ernesto-g/mini_piano/Pictures/1.jpg

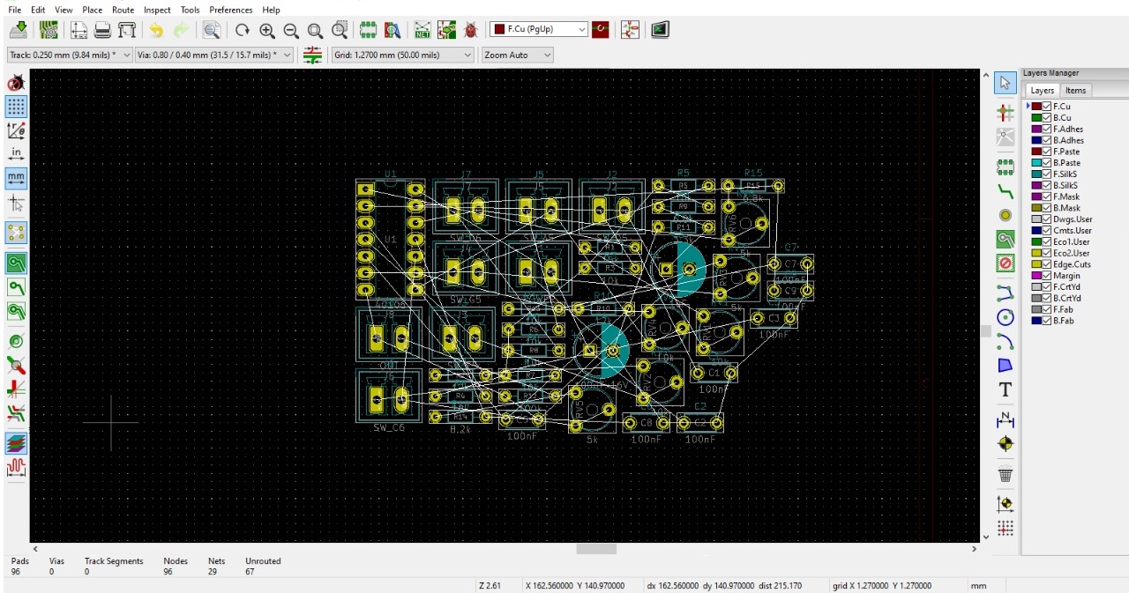
Pictures/1.jpg
