ernesto-g/mini_piano/Pictures/2.jpg

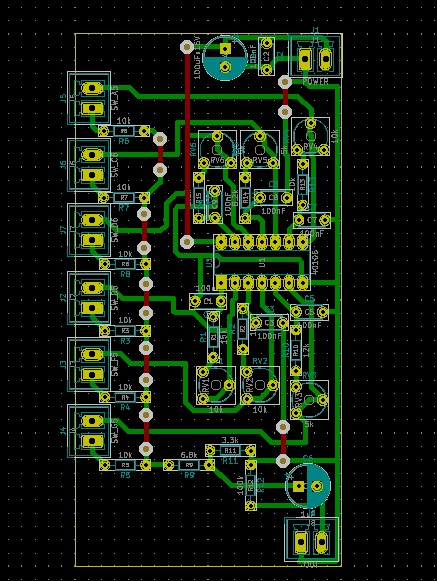
Pictures/2.jpg
