ernesto-g/mini_piano/Pictures/IMG_20210108_180527709.jpg

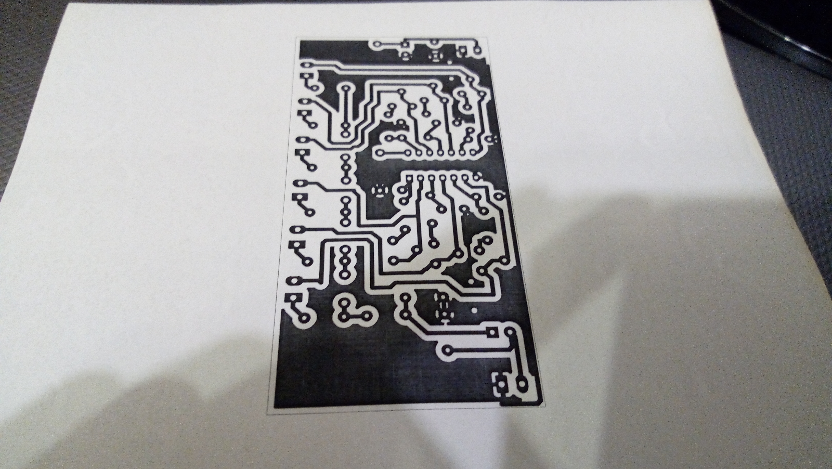
Pictures/IMG_20210108_180527709.jpg
