ernesto-g/mini_piano/Pictures/IMG_20210108_180604123.jpg

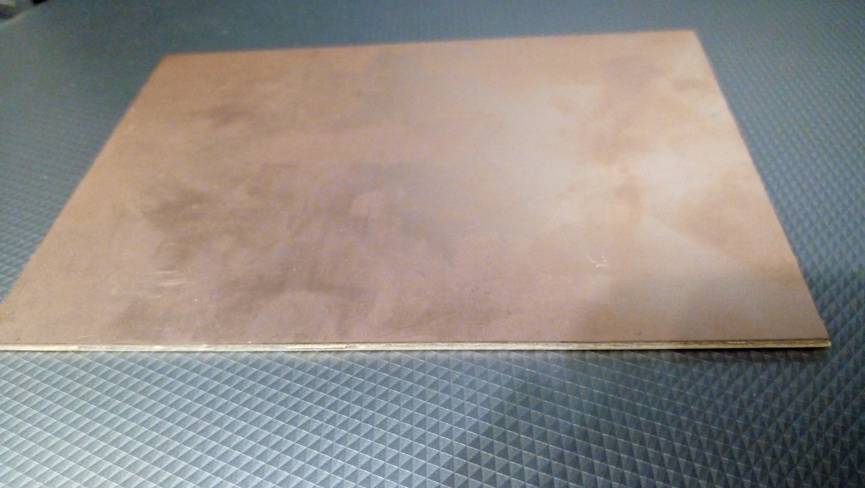
Pictures/IMG_20210108_180604123.jpg
