ernesto-g/mini_piano/Pictures/IMG_20210108_181249977.jpg

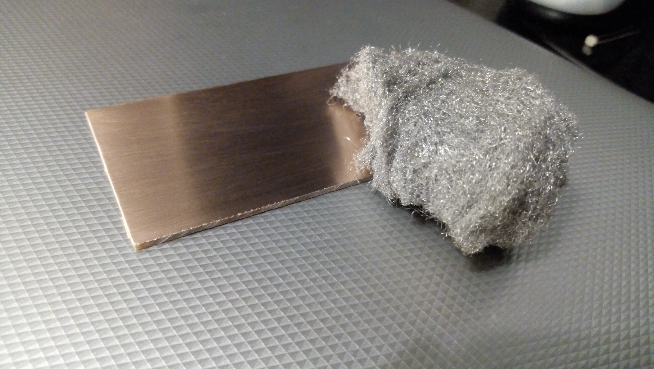
Pictures/IMG_20210108_181249977.jpg
