ernesto-g/mini_piano/Pictures/IMG_20210108_181337347.jpg

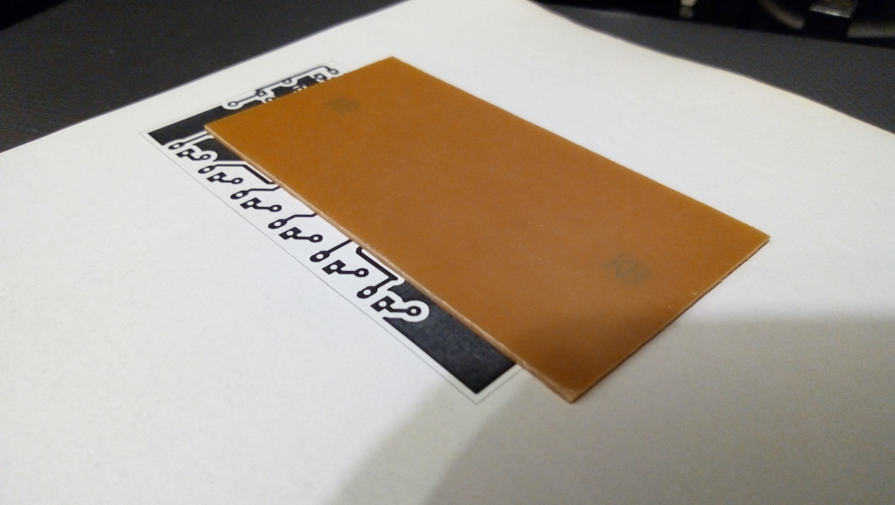
Pictures/IMG_20210108_181337347.jpg
