ernesto-g/mini_piano/Pictures/IMG_20210108_181607837.jpg

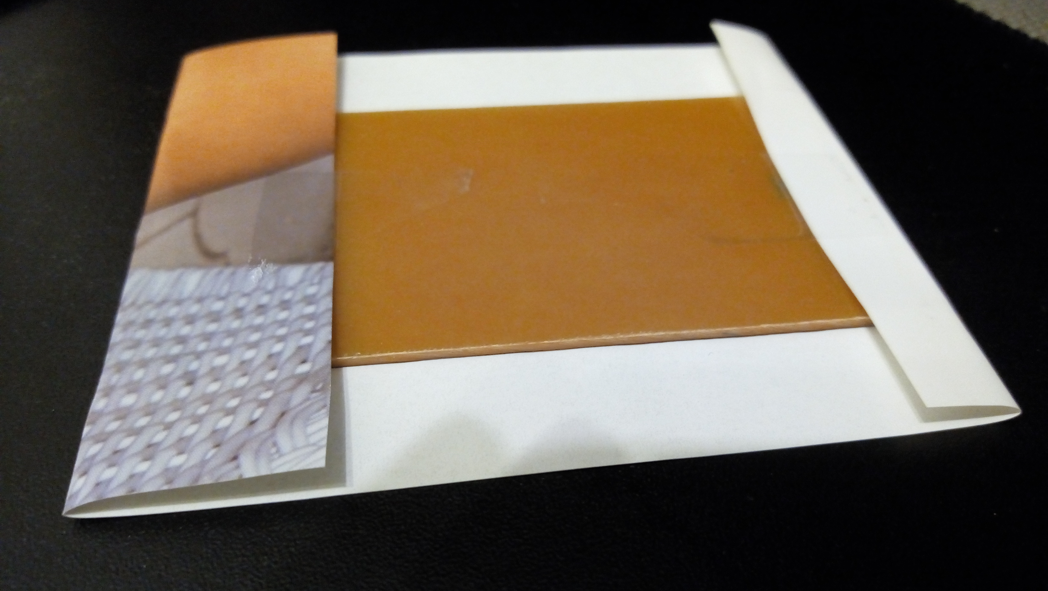
Pictures/IMG_20210108_181607837.jpg
