ernesto-g/mini_piano/Pictures/IMG_20210108_181741189.jpg

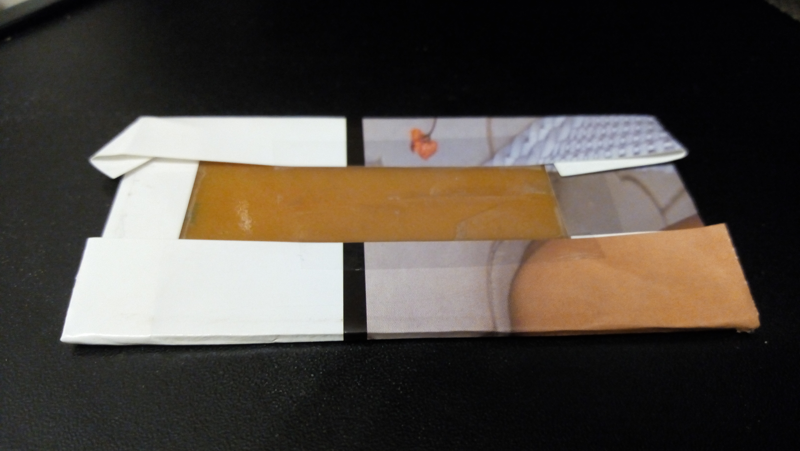
Pictures/IMG_20210108_181741189.jpg
