ernesto-g/mini_piano/Pictures/IMG_20210108_181936412.jpg

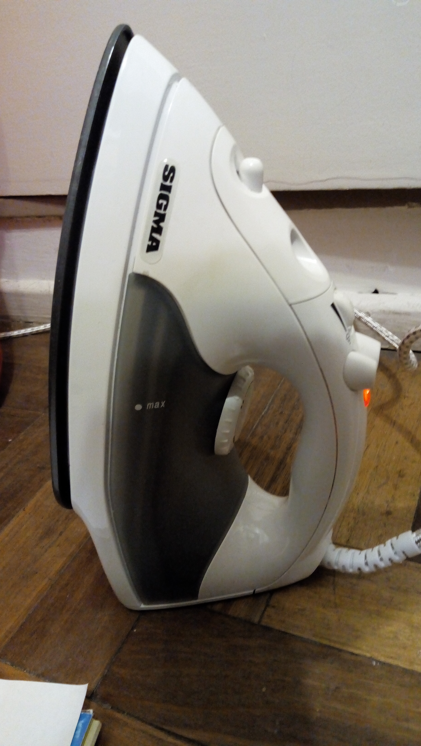
Pictures/IMG_20210108_181936412.jpg
