ernesto-g/mini_piano/Pictures/IMG_20210108_182000813.jpg

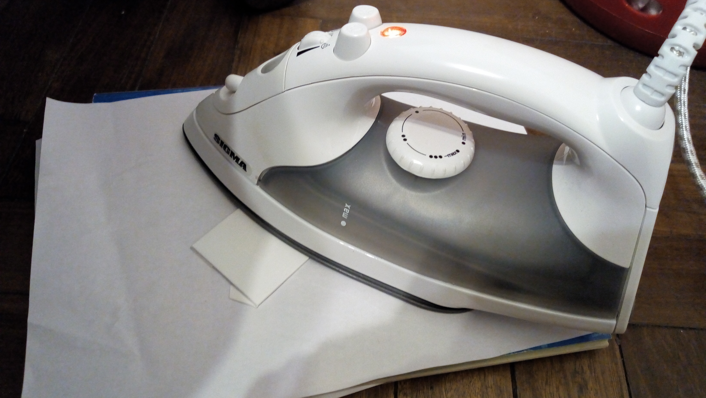
Pictures/IMG_20210108_182000813.jpg
