ernesto-g/mini_piano/Pictures/IMG_20210108_182442168.jpg

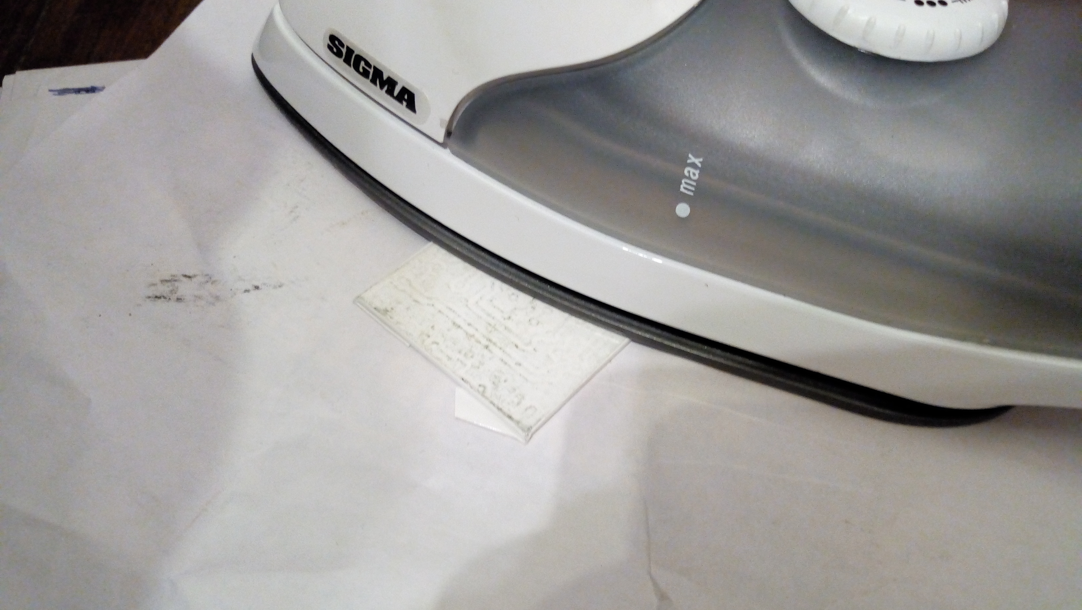
Pictures/IMG_20210108_182442168.jpg
