ernesto-g/mini_piano/Pictures/IMG_20210108_182944492.jpg

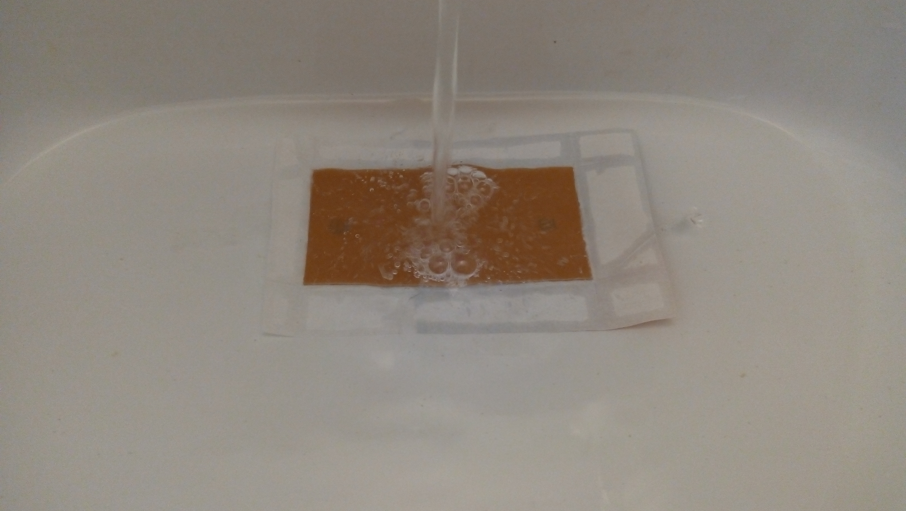
Pictures/IMG_20210108_182944492.jpg
