ernesto-g/mini_piano/Pictures/IMG_20210108_182950383.jpg

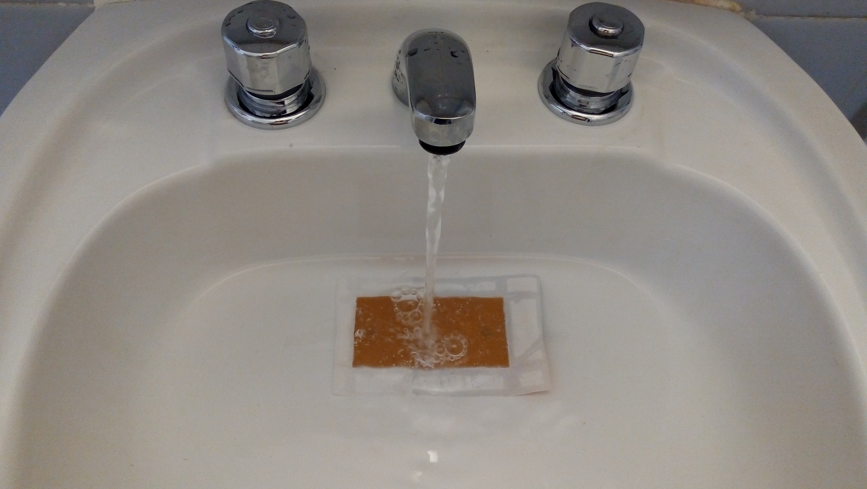
Pictures/IMG_20210108_182950383.jpg
