ernesto-g/mini_piano/Pictures/IMG_20210108_183208809.jpg

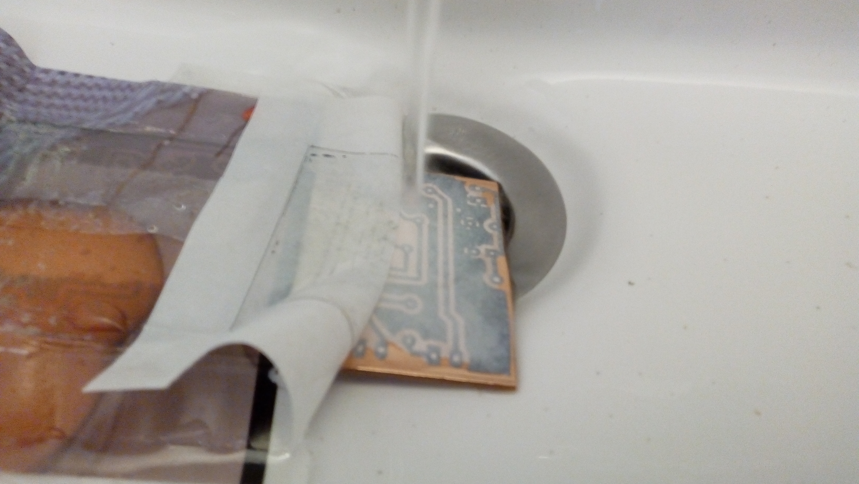
Pictures/IMG_20210108_183208809.jpg
