ernesto-g/mini_piano/Pictures/IMG_20210108_183432457.jpg

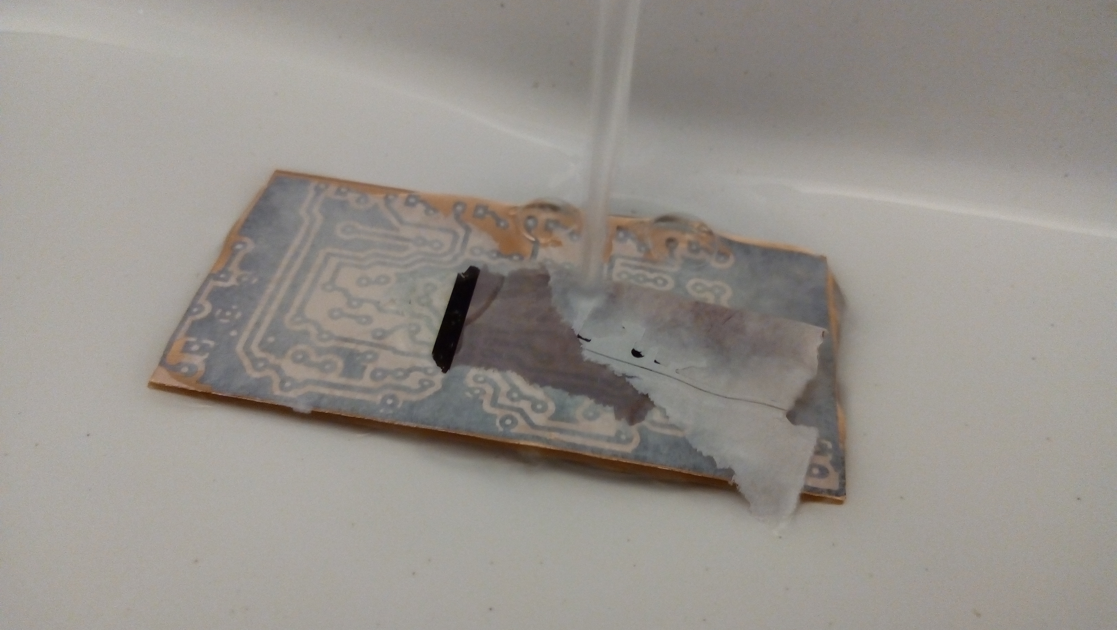
Pictures/IMG_20210108_183432457.jpg
