ernesto-g/mini_piano/Pictures/IMG_20210108_183632835.jpg

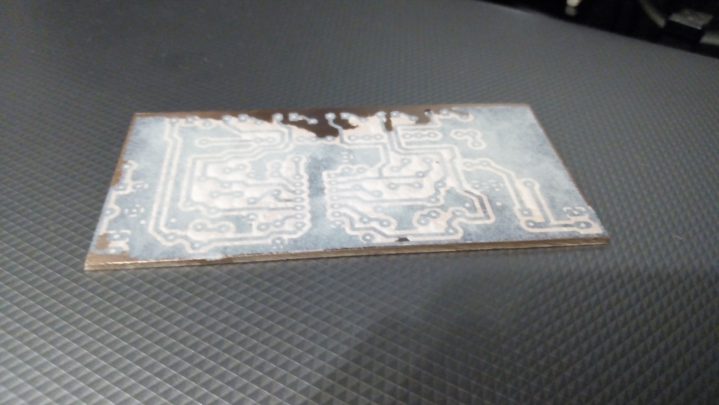
Pictures/IMG_20210108_183632835.jpg
