ernesto-g/mini_piano/Pictures/IMG_20210108_183704219.jpg

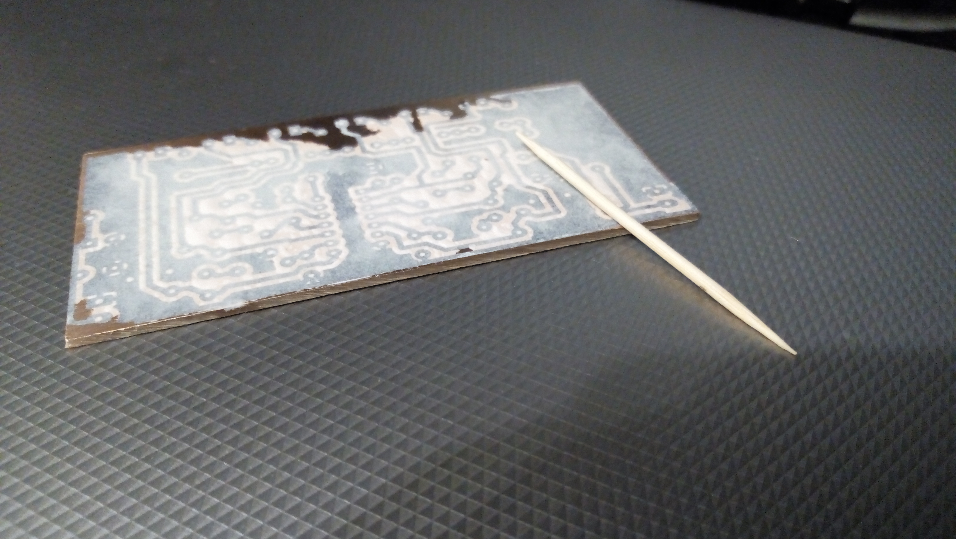
Pictures/IMG_20210108_183704219.jpg
