ernesto-g/mini_piano/Pictures/IMG_20210108_184416622.jpg

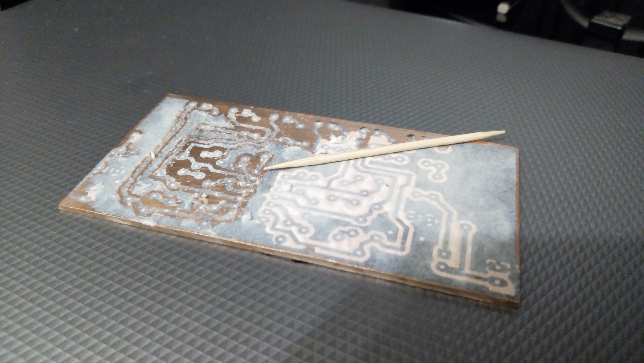
Pictures/IMG_20210108_184416622.jpg
