ernesto-g/mini_piano/Pictures/IMG_20210108_185925848.jpg

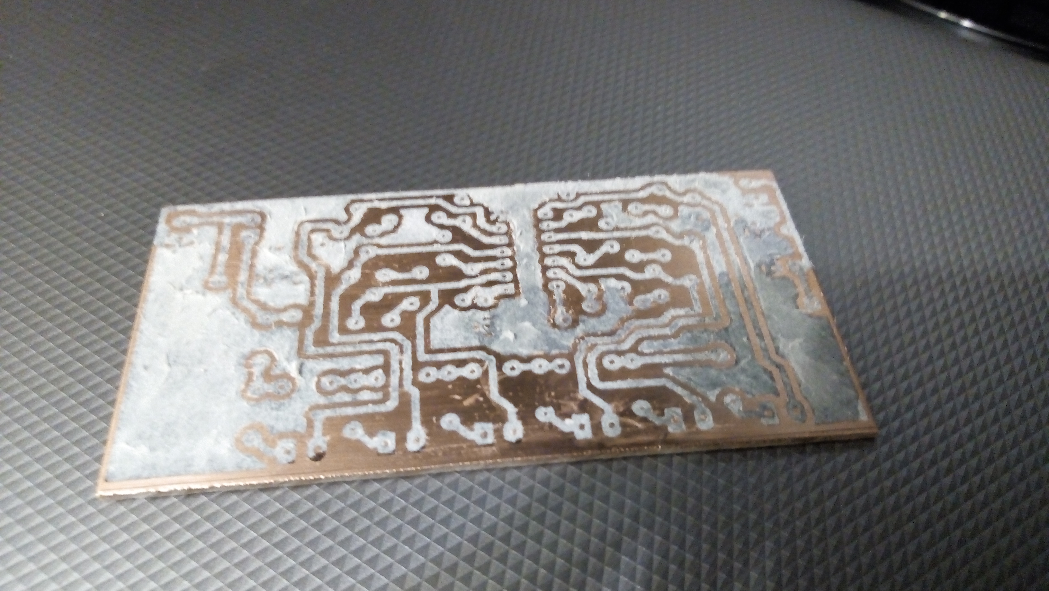
Pictures/IMG_20210108_185925848.jpg
