ernesto-g/mini_piano/Pictures/IMG_20210109_113402439.jpg

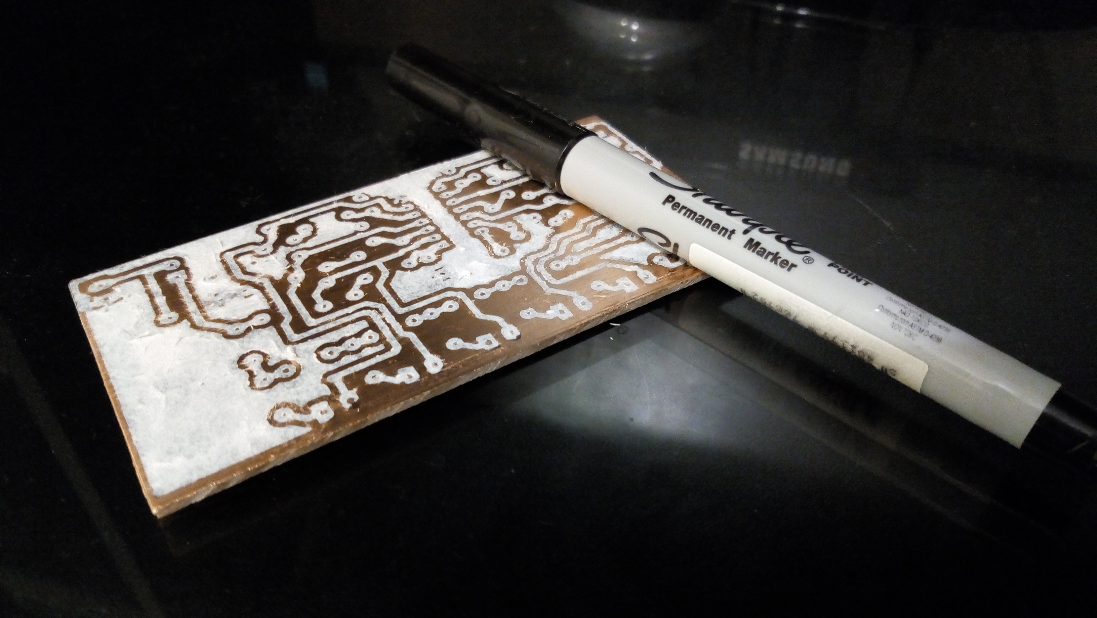
Pictures/IMG_20210109_113402439.jpg
