ernesto-g/mini_piano/Pictures/IMG_20210109_114229073.jpg

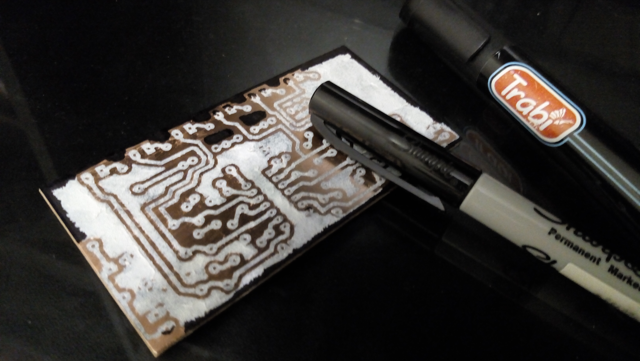
Pictures/IMG_20210109_114229073.jpg
