ernesto-g/mini_piano/Pictures/IMG_20210109_114355224.jpg

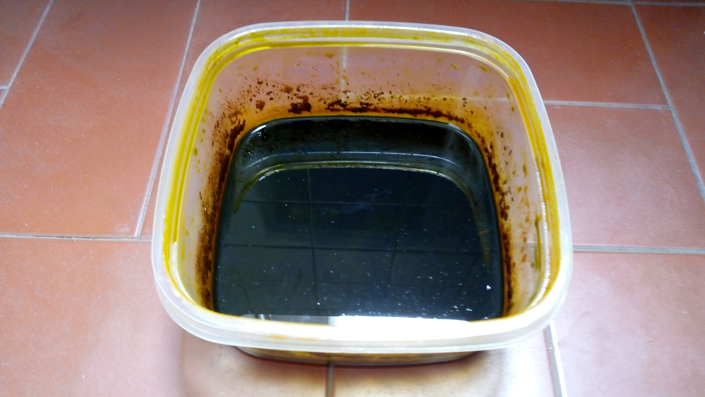
Pictures/IMG_20210109_114355224.jpg
