ernesto-g/mini_piano/Pictures/IMG_20210109_114416226.jpg

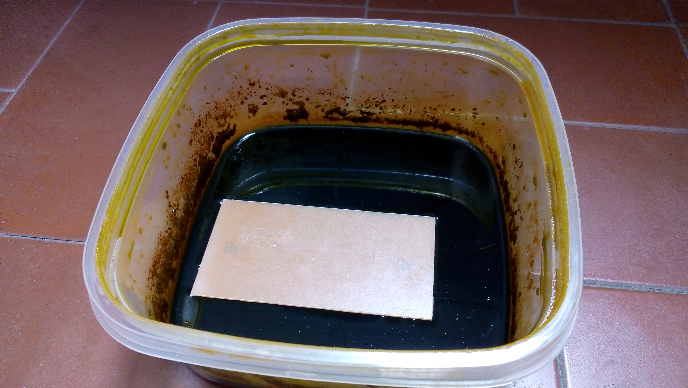
Pictures/IMG_20210109_114416226.jpg
