ernesto-g/mini_piano/Pictures/IMG_20210109_122817724.jpg

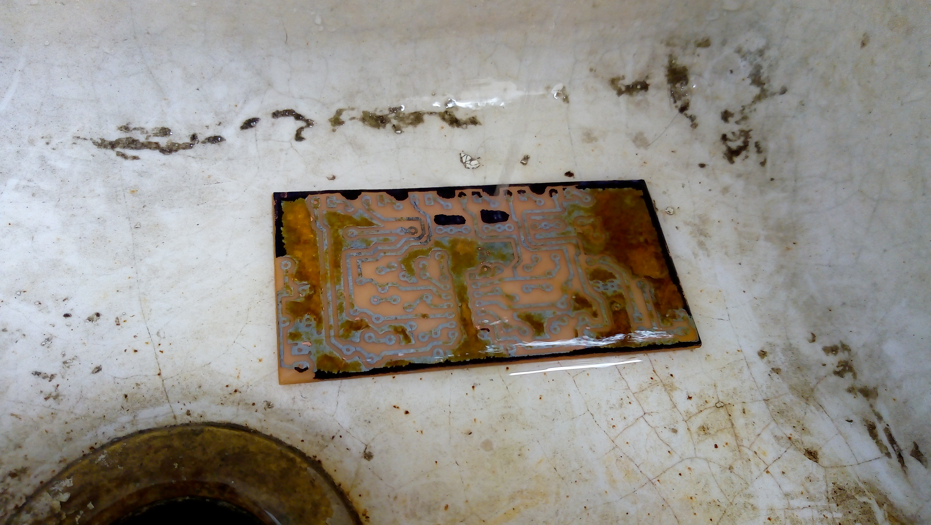
Pictures/IMG_20210109_122817724.jpg
