ernesto-g/mini_piano/Pictures/IMG_20210109_123030492.jpg

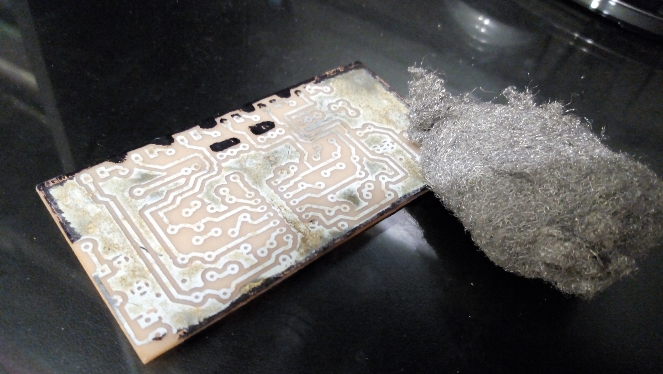
Pictures/IMG_20210109_123030492.jpg
