ernesto-g/mini_piano/Pictures/IMG_20210109_123859995.jpg

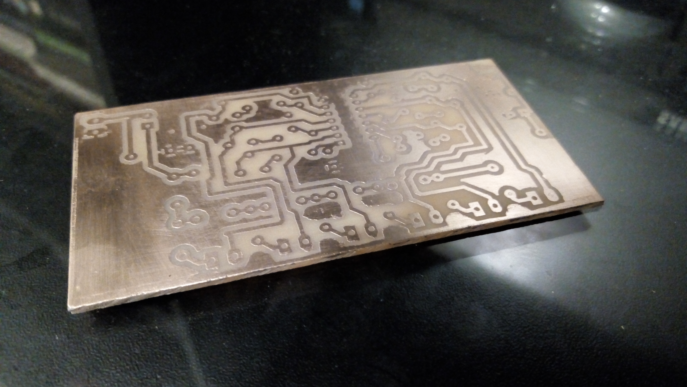
Pictures/IMG_20210109_123859995.jpg
