ernesto-g/mini_piano/Pictures/IMG_20210109_123930578.jpg

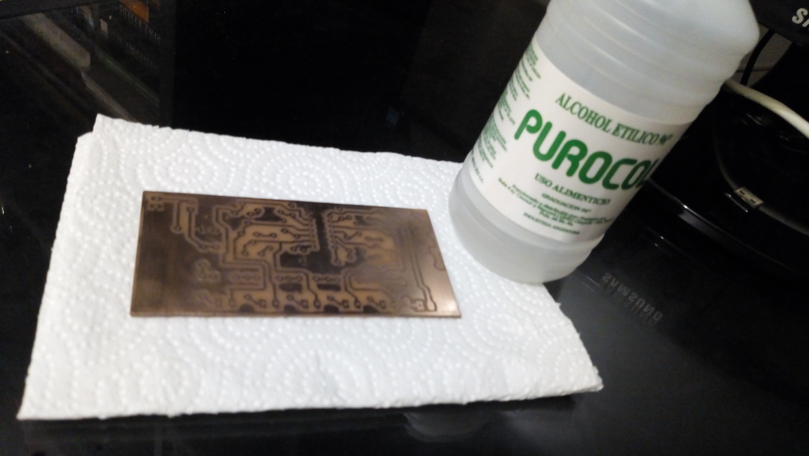
Pictures/IMG_20210109_123930578.jpg
