ernesto-g/mini_piano/Pictures/IMG_20210109_124137653.jpg

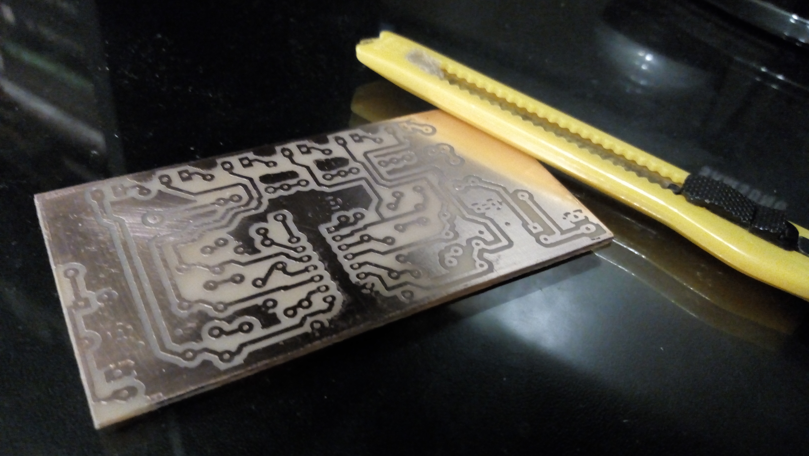
Pictures/IMG_20210109_124137653.jpg
