ernesto-g/mini_piano/Pictures/IMG_20210109_124410188.jpg

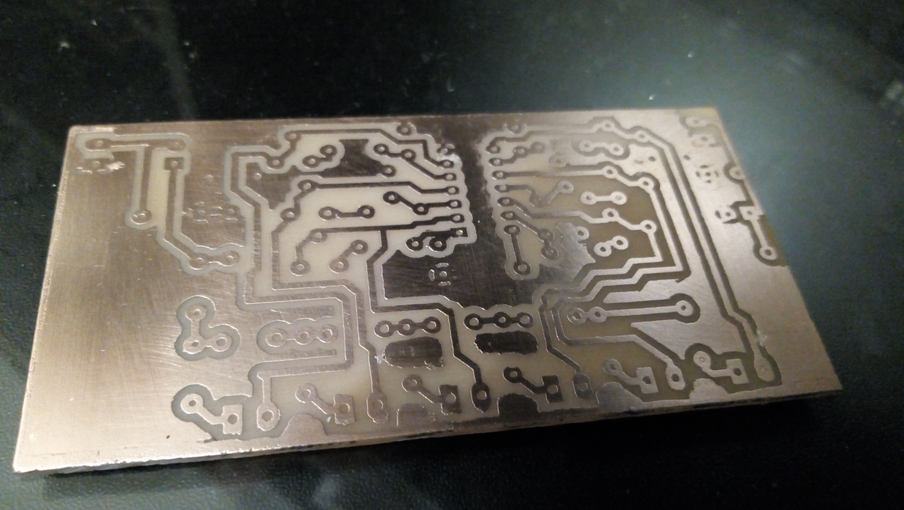
Pictures/IMG_20210109_124410188.jpg
