ernesto-g/mini_piano/Pictures/IMG_20210110_175810726.jpg

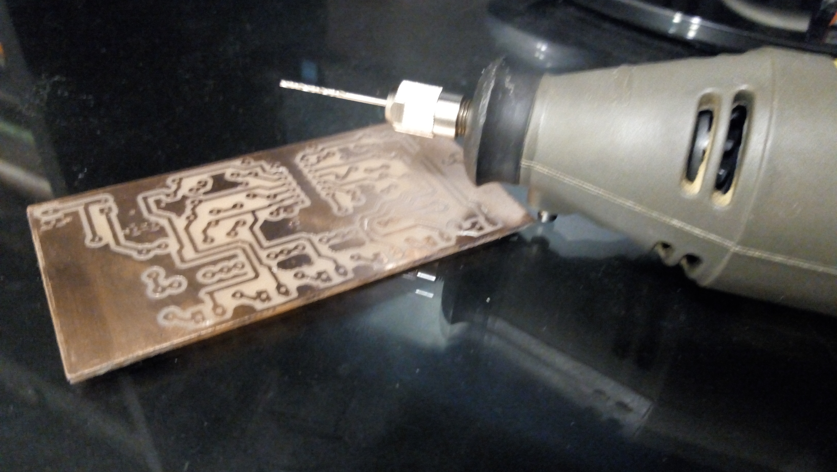
Pictures/IMG_20210110_175810726.jpg
