ernesto-g/mini_piano/Pictures/IMG_20210110_181046374.jpg

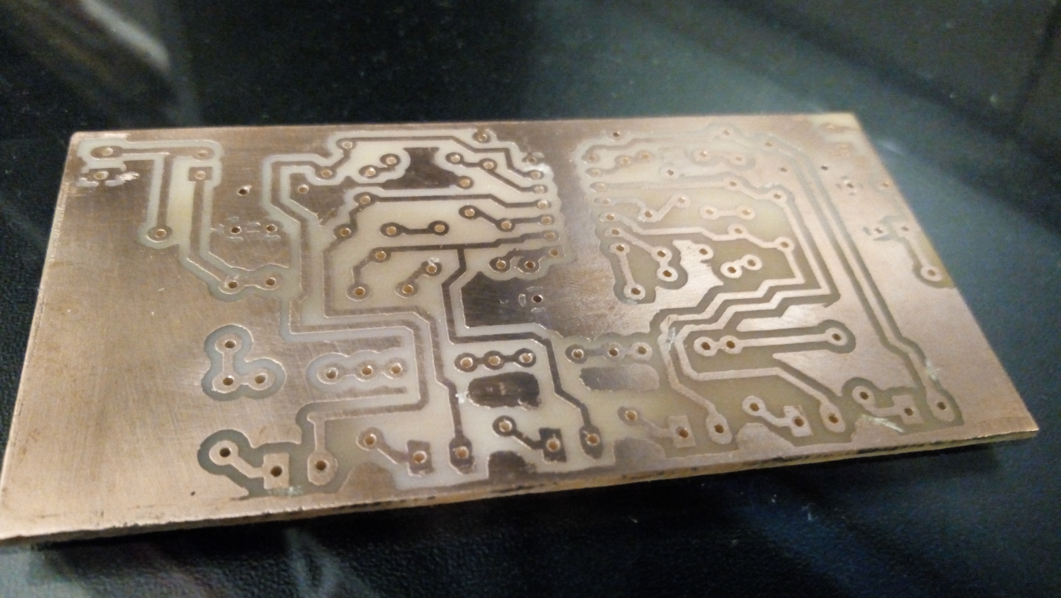
Pictures/IMG_20210110_181046374.jpg
