ernesto-g/mini_piano/Pictures/IMG_20210110_181058971.jpg

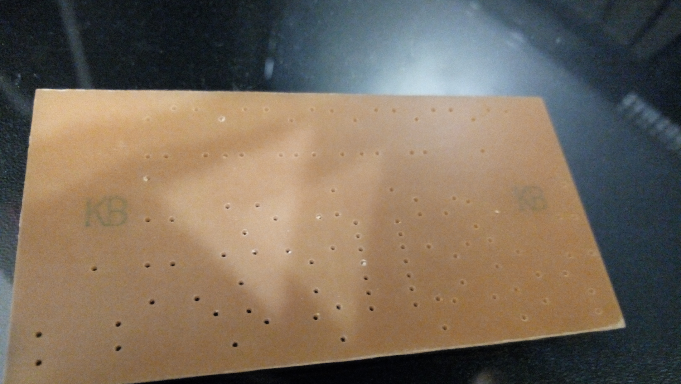
Pictures/IMG_20210110_181058971.jpg
