ernesto-g/mini_piano/Pictures/IMG_20210110_181122908.jpg

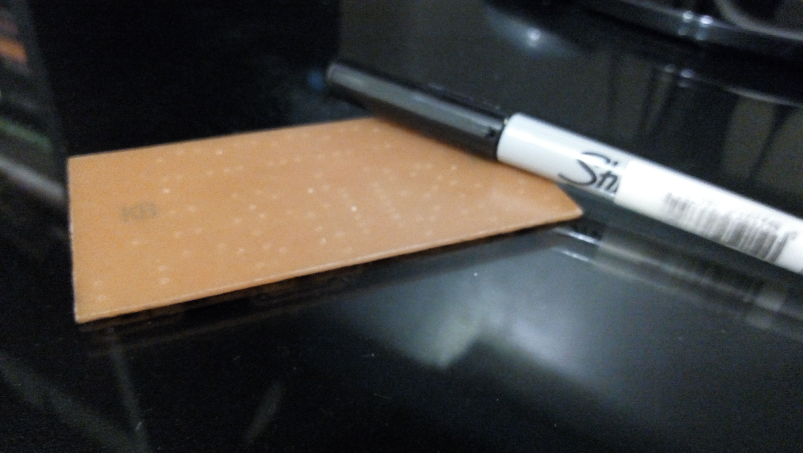
Pictures/IMG_20210110_181122908.jpg
